tube0013/tube_gateways/models/current/tubeszb-router/firmware/readme.md

# Changes:

All fw are based on stock Z-Stack FW (https://github.com/Koenkk/Z-Stack-firmware/tree/master/router/Z-Stack_3.x.0) with minimal changes - led control and tubeszb branding

**tubeszb_CC1352P2_CC2652P_launchpad_router_20221102**

Sync with upstream z-stack

changes: enable led on boot of fw, add product_label and product_url attributes in basic cluster - device works with main z2m ti.router converter and ZHA ti.router quirk.

**Earlier versions**

20220223:
sycnc with z-stack, adding led and updateing model/manufacturer attributes.

20220111:

Model Id and Manufacturer:

Application/zcl_genericapp.c:

Lines 98-100
```
const uint8_t zclGenericApp_ManufacturerName[] = { 7, 'T','u','b','e','s','Z','B' };
const uint8_t zclGenericApp_ModelID[] = { 14, 't','u','b','e','s','z','b','.','r','o','u','t','e','r' };
const uint8_t zclGenericApp_SwBuildID[] = { 8, '2','0','2','2','0','1','1','1' };
```

Always on LED:

/syscfg/ti_drivers_config.c:

Line: 240:

```
    GPIOCC26XX_DIO_06 | GPIO_CFG_OUT_STD | GPIO_CFG_OUT_STR_MED | GPIO_CFG_OUT_HIGH,
```

TX 9 db:

/Stack/Config/f8wrouter.opts:

Added:

```
-DPHY_TX_POWER_FREQ_2_4_G=9

```
