tube0013/tube_gateways/models/current/tubeszb-cc2652-P7-poe-2023/firmware/esphome/README.md

## Notice

The ESPHome configs in this folder are superseded by the TubesZB-ESPHome-Builder repository.
The YAMLs here are kept for historical reference and are not expected to compile with current ESPHome versions.
Use the manifest for this device:
Manifest filename: `tubeszb-cc2652p7-poe-2023.yaml`
- [tubeszb-cc2652p7-poe-2023.yaml](https://github.com/tube0013/TubesZB-ESPHome-Builder/blob/main/manifests/tubeszb-cc2652p7-poe-2023.yaml)

# ESP32 Flashing

Firmware is available in this folder.

Recommend the ESPHome Flasher tool:
https://github.com/esphome/esphome-flasher/releases

Windows will require the CH340 Serial driver. A version can be found [downloaded here](https://www.olimex.com/Products/Breadboarding/BB-CH340T/resources/CH341SER.zip)

Partially removed the board from the case to access the microUSB port on the Olimex ESP32-PoE module. Use a USB cable (not power only) to connect the the board to the computer doing the flashing. Reminder do not connect USB and Powered ethernet concurrently.

After the flashing completes the esp32 will automatically reset and boot the new FW while showing the console in the flashing tool window to confirm it was flashed okay.

## ESPHome-flasher 

Fire up the flasher and select the correct port and point it to the downloaded FW bin:

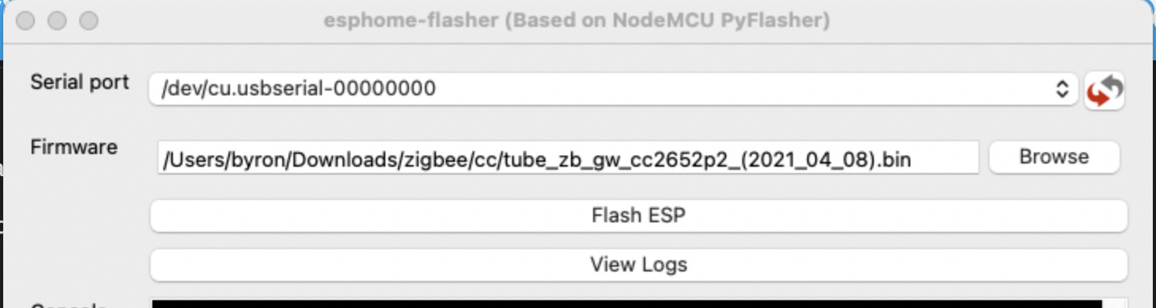
[picture p26: images/esphome_flasher_1.jpg]
  

Hit flash, and you should see something like this:

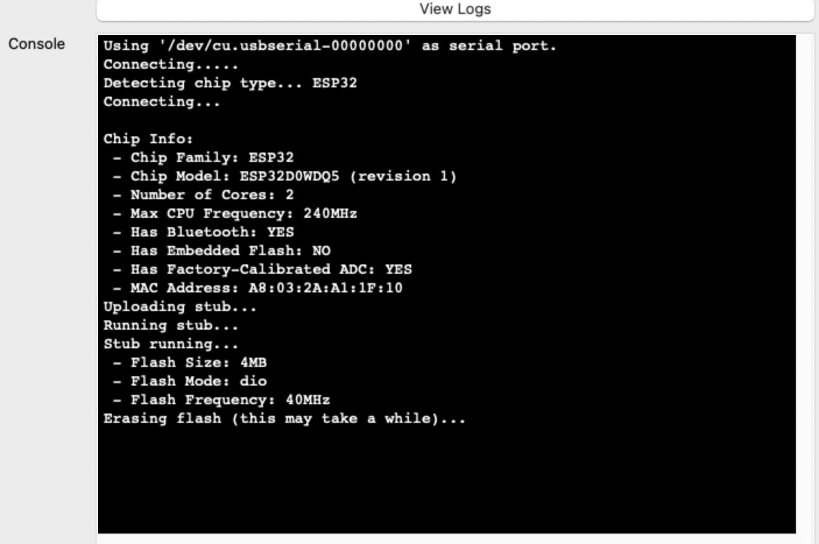
[picture p27: images/esphome_flasher_2.jpg]
  

after about a minute or so:

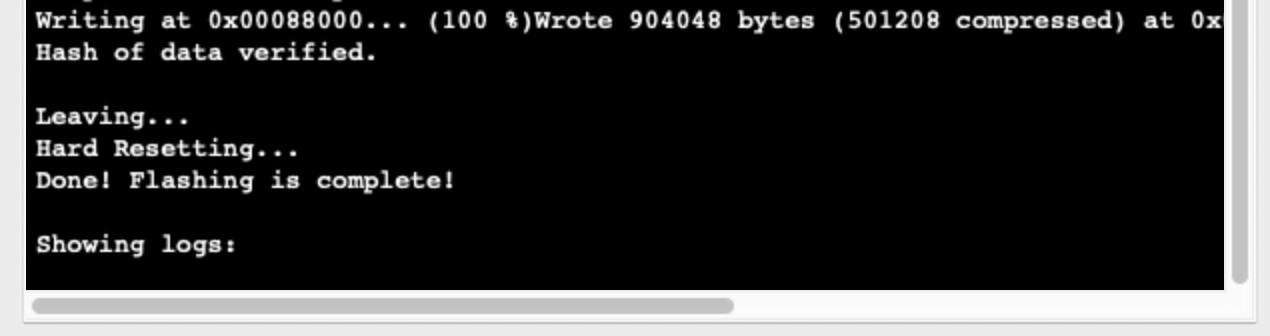
[picture p28: images/esphome_flasher_3.jpg]
