tube0013/tube_gateways/models/current/tubeszb-cc2652-P7-poe-2023/firmware/CC2652/readme.md

## CC2652 P7 Coordinator Firmware 

Firmware for the CC2652 P7 (CC1352P7_coordinator_*.zip) is available from the Z-Stack Firmware Repository:

https://github.com/Koenkk/Z-Stack-firmware/tree/master/coordinator/Z-Stack_3.x.0/bin

Coordinators use the lauchpad variant with BSL Trigger on DIO_15 and LEDs on DIO_6 and DIO_7
