tube0013/tube_gateways/models/current/tubeszb-efr32-MGM210-poe/firmware/esphome/README.md

ESPHome yaml and binaries for TubesZB EFR32 MGM21 PoE Coordinators.

2022 and 2023 models are different, use the yaml/binary for your model.
