tube0013/tube_gateways/models/current/tubeszb-cc2652-eth_usb/firmware/esphome/previous_versions/readme.md

Note currently ESPHome Releases 2021.10 and forward do not have reliable serial connections to the zigbee module exhibiting in frequent (every few hours) disconnections. 

Compile with 2021.9 versions for reliable operation.
