tube0013/tube_gateways/images/add_integration.png

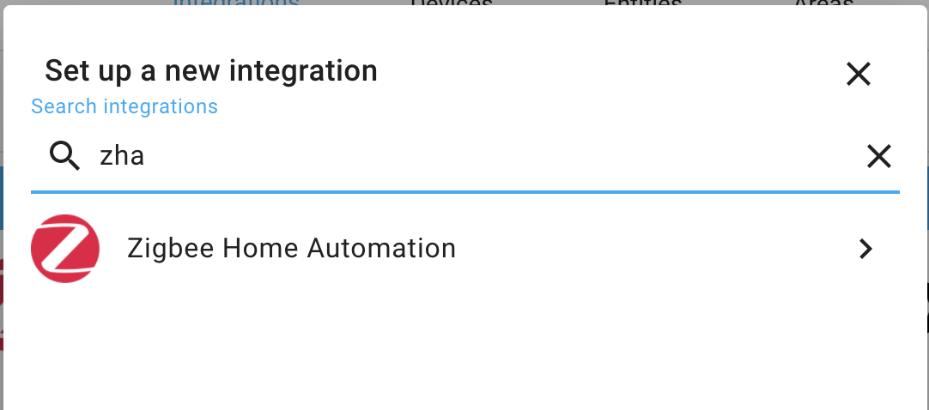
images/add_integration.png
