tube0013/tube_gateways/images/cc2652_connection.png

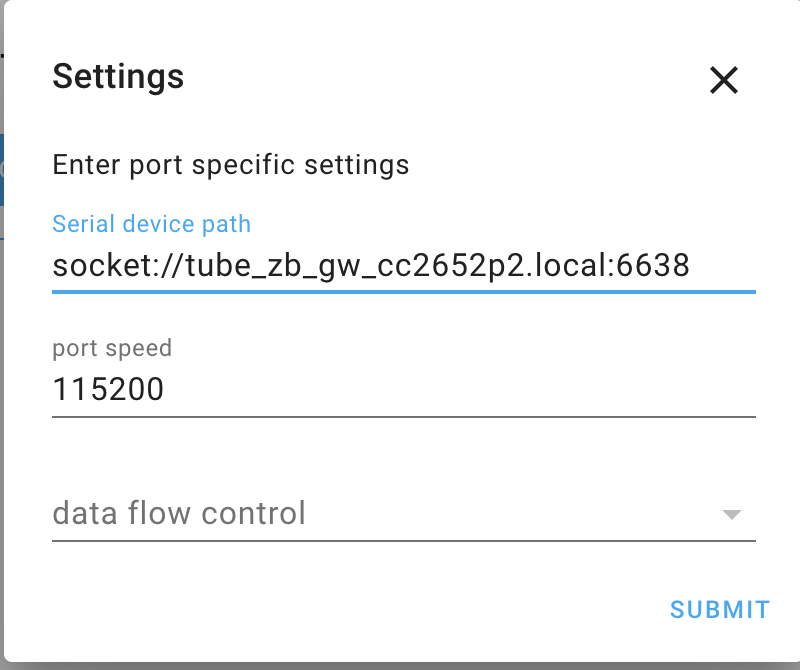
images/cc2652_connection.png
