tube0013/tube_gateways/images/efr32_connection.png

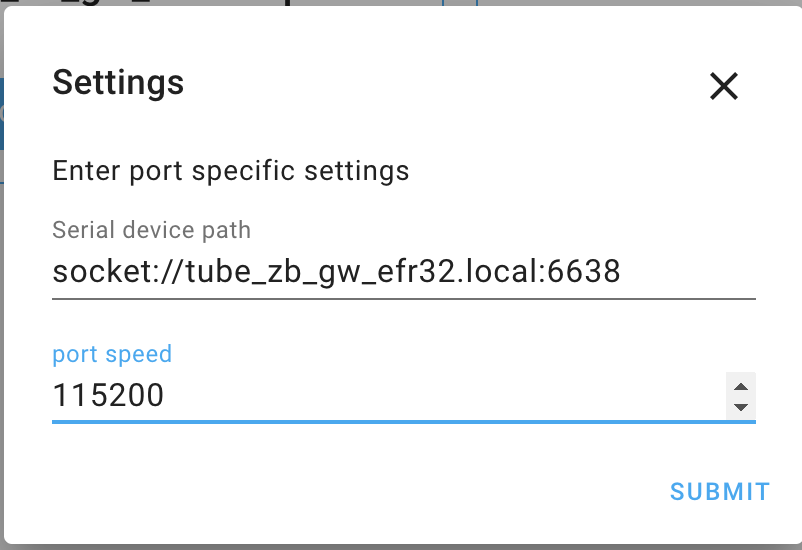
images/efr32_connection.png
