tube0013/tube_gateways/images/esphome1.png

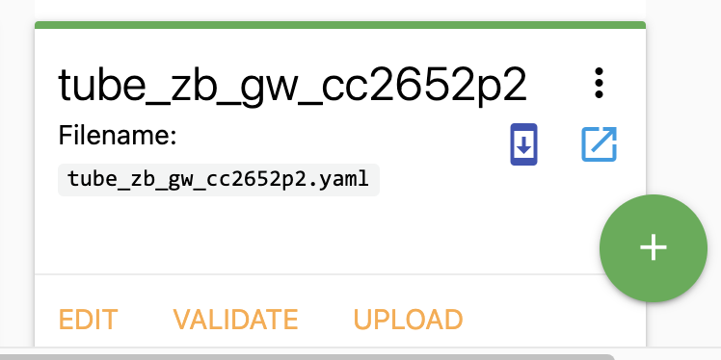
images/esphome1.png
