tube0013/tube_gateways/images/esphome_ota.png

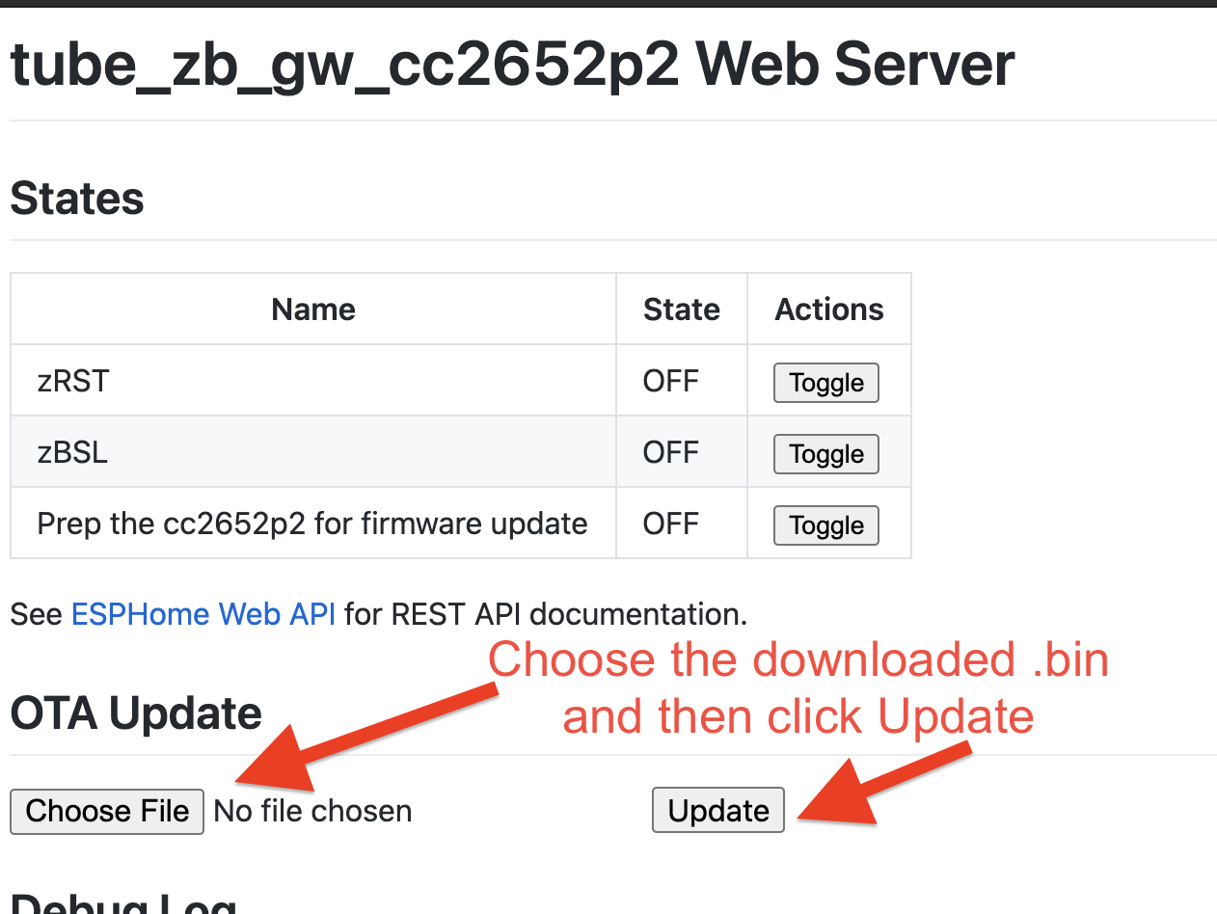
images/esphome_ota.png
