tube0013/tube_gateways/images/radio_type.png

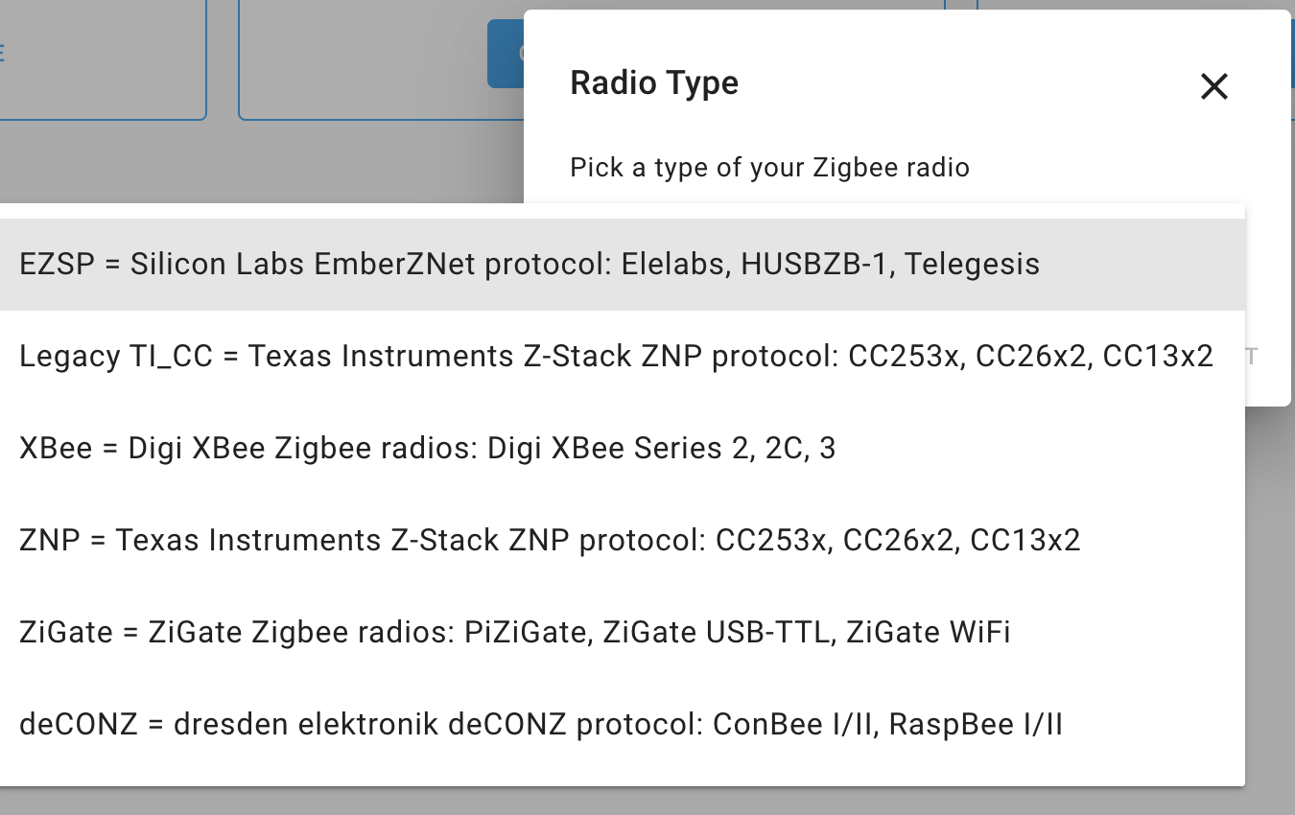
images/radio_type.png
