tube0013/tube_gateways/models/current/tubeszb-router/case/usermods/cover over usb power.jpg

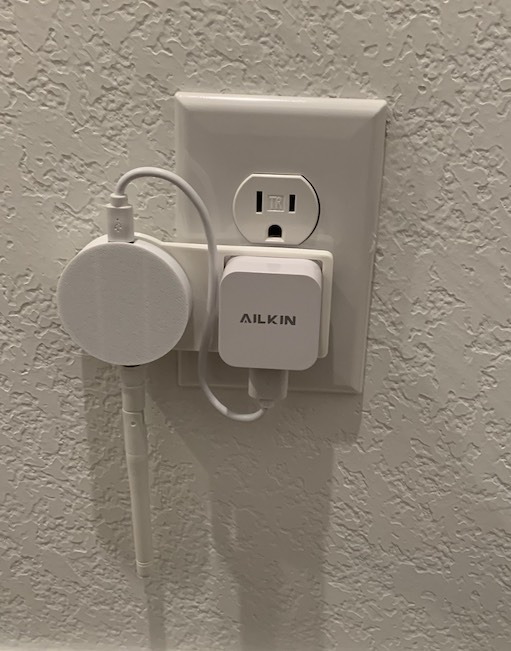
models/current/tubeszb-router/case/usermods/cover over usb power.jpg
