tube0013/tube_gateways/models/current/tubeszb-wt32-eth01-bt-kit/images/Subject 2.png

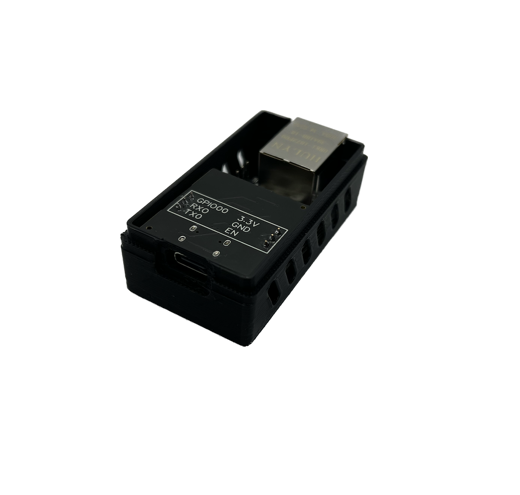
models/current/tubeszb-wt32-eth01-bt-kit/images/Subject 2.png
