tube0013/tube_gateways/models/current/tubeszb-dual-radio-kit/case/tubeszb_dual-radio_top_2025.stl

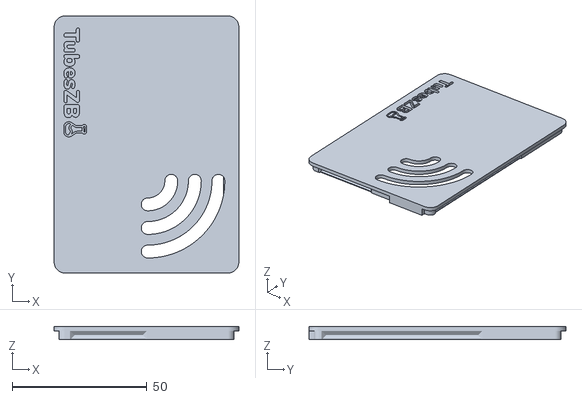
[picture p61: CAD file, 2025-07-22]
models/current/tubeszb-dual-radio-kit/case/tubeszb_dual-radio_top_2025.stl
68.4 x 95.2 x 4.80
