tube0013/tube_gateways/models/current/tubeszb-efr32-MGM12-eth_usb/case/tubeszb-cc2652-eth_usb_top.stl

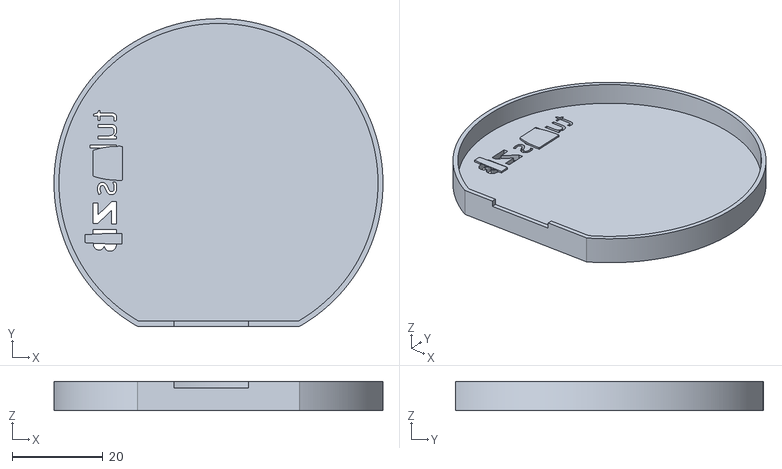
[picture p62: CAD file, 2022-01-12]
models/current/tubeszb-efr32-MGM12-eth_usb/case/tubeszb-cc2652-eth_usb_top.stl
72.4 x 67.7 x 6.40
