tube0013/tube_gateways/models/current/tubeszb-efr32-MGM210-poe/case/Step_Fusion360/TubesZB_2022_PoE_Coordinator_Case.step

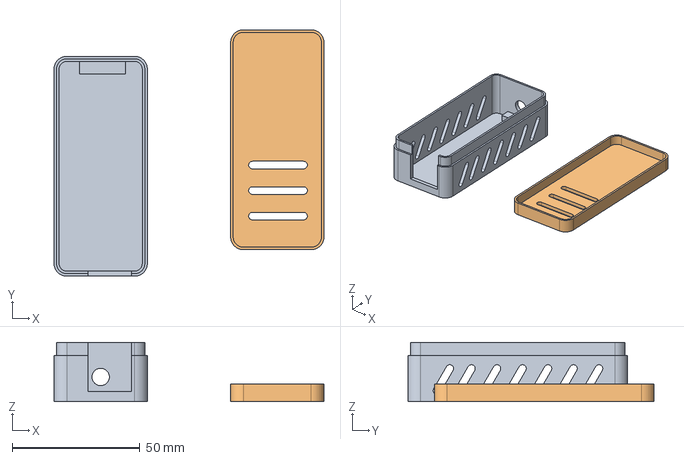
[picture p63: CAD file, 2022-06-28]
models/current/tubeszb-efr32-MGM210-poe/case/Step_Fusion360/TubesZB_2022_PoE_Coordinator_Case.step
105.8 x 96.6 x 23.2 mm
