tube0013/tube_gateways/models/current/tubeszb-router/case/tubesZB_router_bottom_v12.stl

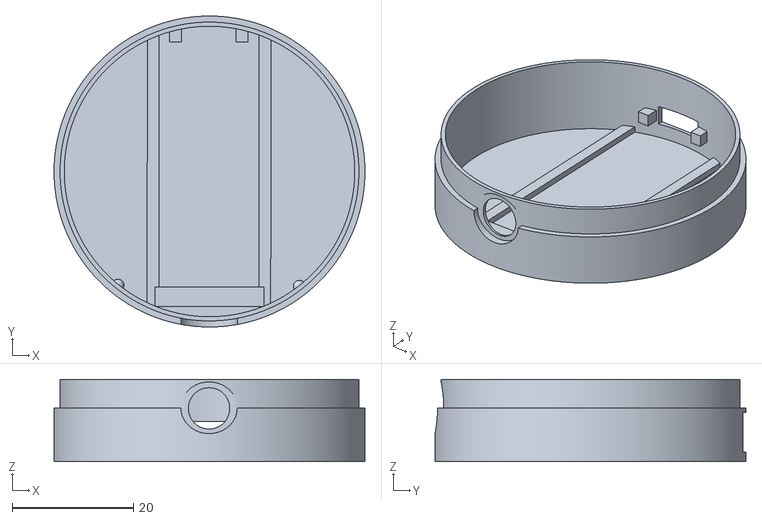
[picture p64: CAD file, 2023-06-05]
models/current/tubeszb-router/case/tubesZB_router_bottom_v12.stl
51.2 x 51.2 x 13.5
