tube0013/tube_gateways/models/current/tubeszb-zw-kit/Case/Z-Wave_PoE_Top.stl

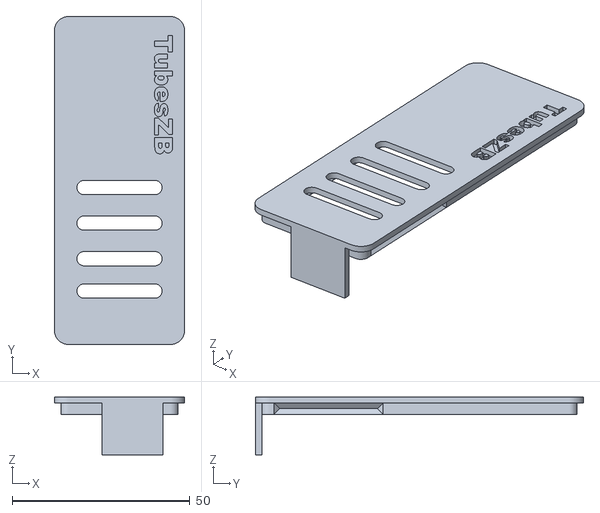
[picture p65: CAD file, 2024-04-16]
models/current/tubeszb-zw-kit/Case/Z-Wave_PoE_Top.stl
36.6 x 92.2 x 16.2
