tube0013/tube_gateways/tube_poe_coordinator/PoE2_Bottom_v0.1c.stl

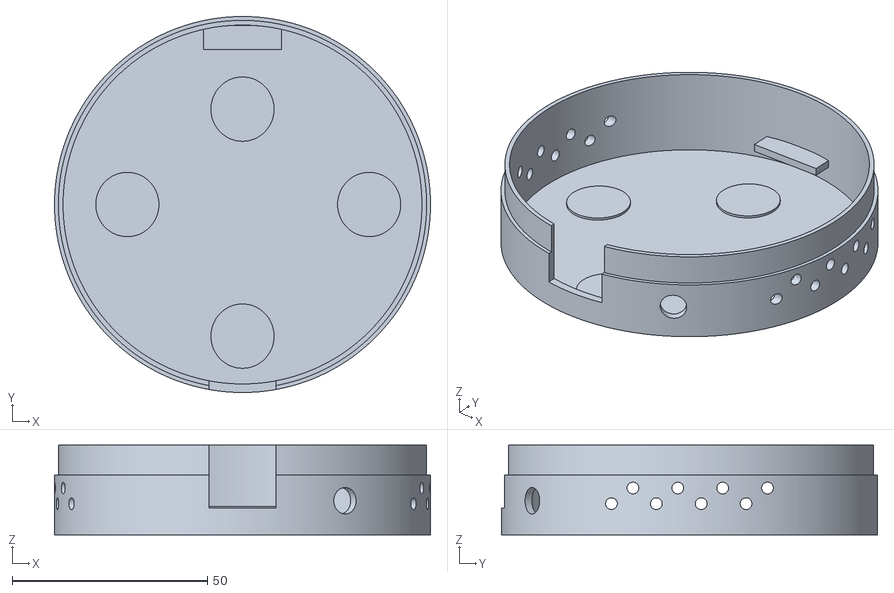
[picture p66: CAD file, 2021-11-03]
tube_poe_coordinator/PoE2_Bottom_v0.1c.stl
96.4 x 96.4 x 23.0
