tube0013/tube_gateways/tube_usb_cc_coordinator/STL_files/cc_usb_cord_Bottom_v0.5b.stl

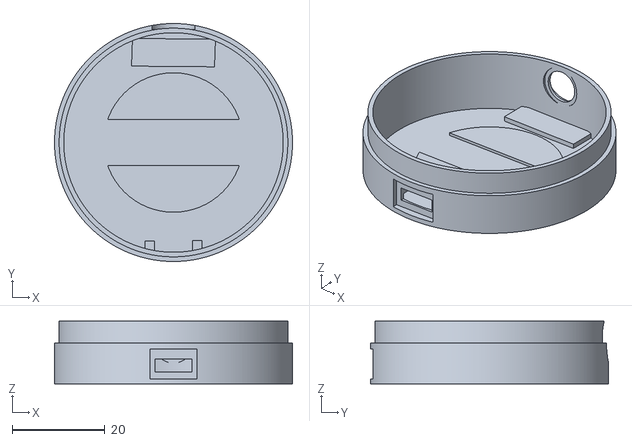
[picture p67: CAD file, 2021-05-03]
tube_usb_cc_coordinator/STL_files/cc_usb_cord_Bottom_v0.5b.stl
51.2 x 51.2 x 13.5
