tube0013/tube_gateways/models/current/tubeszb-efr32-MGM210-poe/case/tubeszb-cc2652-poe-2022_Top.stl

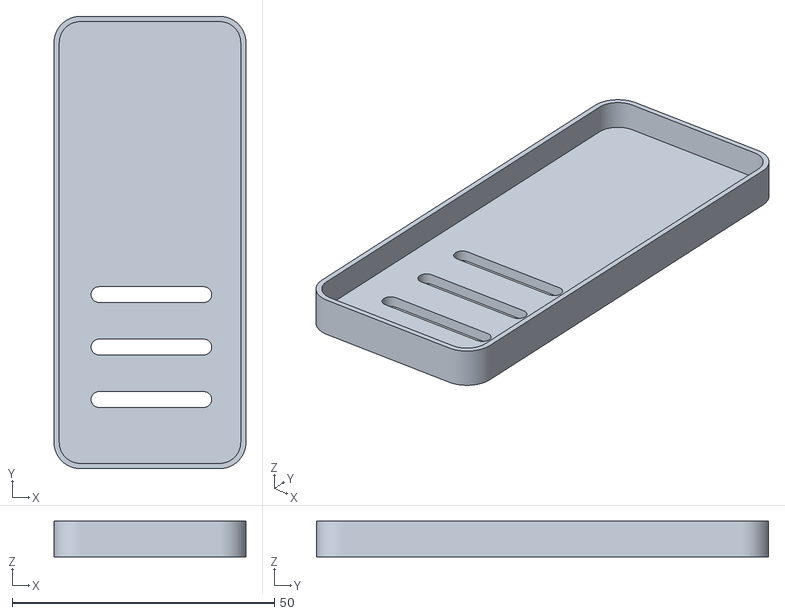
[picture p68: CAD file, 2022-07-27]
models/current/tubeszb-efr32-MGM210-poe/case/tubeszb-cc2652-poe-2022_Top.stl
36.6 x 86.2 x 6.80
