tube0013/tube_gateways/models/current/tubeszb-router/case/cc_router_bot_v11.stl

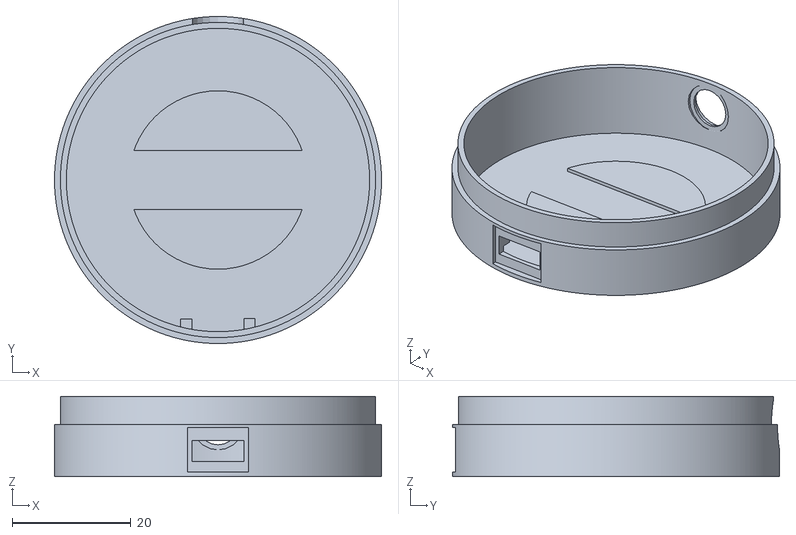
[picture p69: CAD file, 2021-03-17]
models/current/tubeszb-router/case/cc_router_bot_v11.stl
55.0 x 55.0 x 13.5
