tube0013/tube_gateways/models/current/tubeszb-efr32-MGM210-poe/case/tubeszb-cc2652-poe-2022_Bot.stl

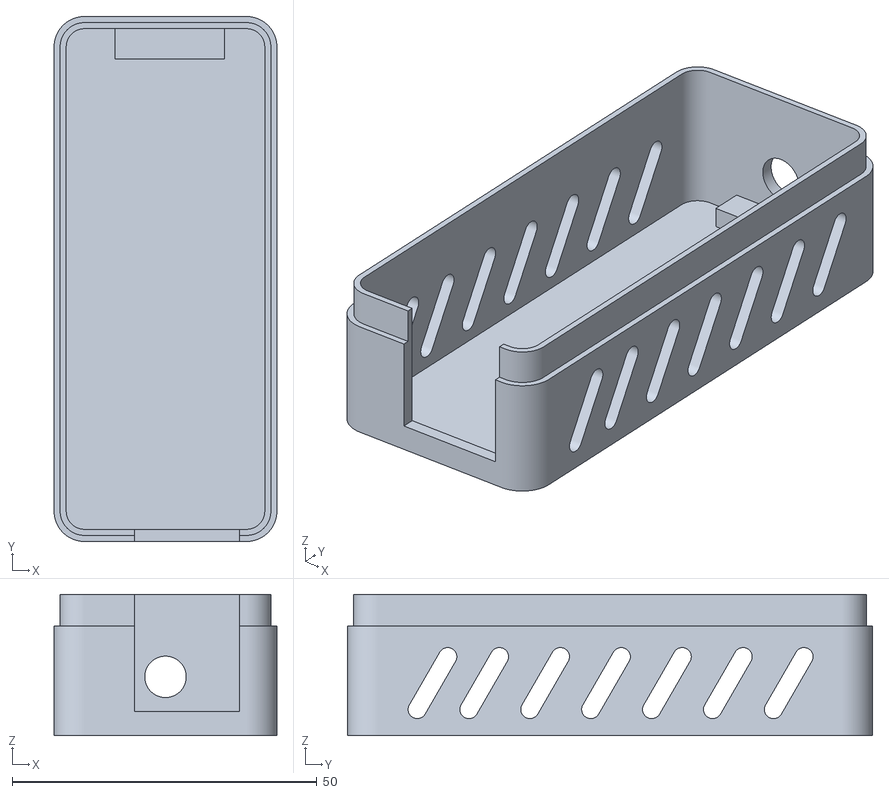
[picture p70: CAD file, 2022-07-27]
models/current/tubeszb-efr32-MGM210-poe/case/tubeszb-cc2652-poe-2022_Bot.stl
36.6 x 86.2 x 23.2
